ldab/reflow-solder-hot-plate/version.py

import subprocess

Import("env")

def get_firmware_specifier_build_flag():
    ret = subprocess.run(["git", "describe", "--tags", "--always", "--dirty"], stdout=subprocess.PIPE, text=True) #Uses only annotated tags
    build_version = ret.stdout.strip()
    build_flag = "-D VERSION=\\\"" + build_version + "\\\""
    print ("Firmware Version: " + build_version)
    return (build_flag)

env.Append(
    BUILD_FLAGS=[get_firmware_specifier_build_flag()]
)
